satorusaka/Ongeki-Con/WAD assembly/STLs/WAD - Cover.3mf

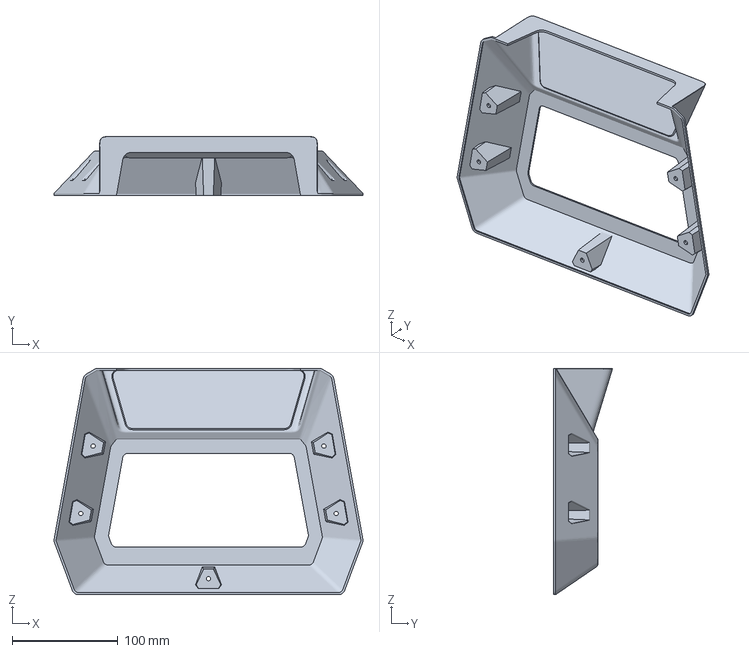
[picture p21: CAD file, 2023-08-07]
WAD assembly/STLs/WAD - Cover.3mf
292.7 x 55.8 x 214.4 mm
