satorusaka/Ongeki-Con/Swing assembly/STLs/Knob_L.3mf

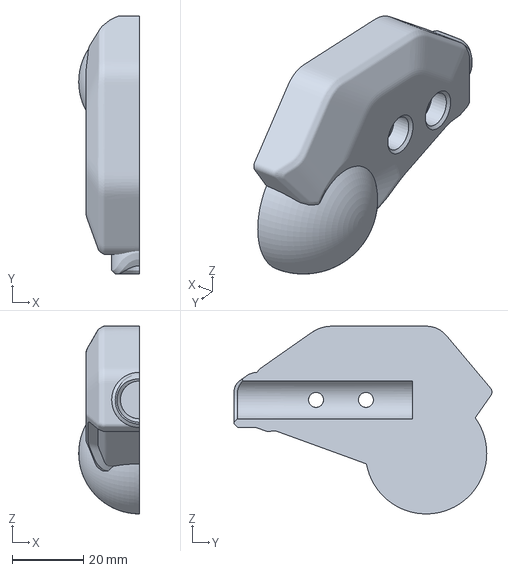
[picture p22: CAD file, 2023-09-01]
Swing assembly/STLs/Knob_L.3mf
17.0 x 72.3 x 52.7 mm
