satorusaka/Ongeki-Con/Swing assembly/STLs/T-Coupler.3mf

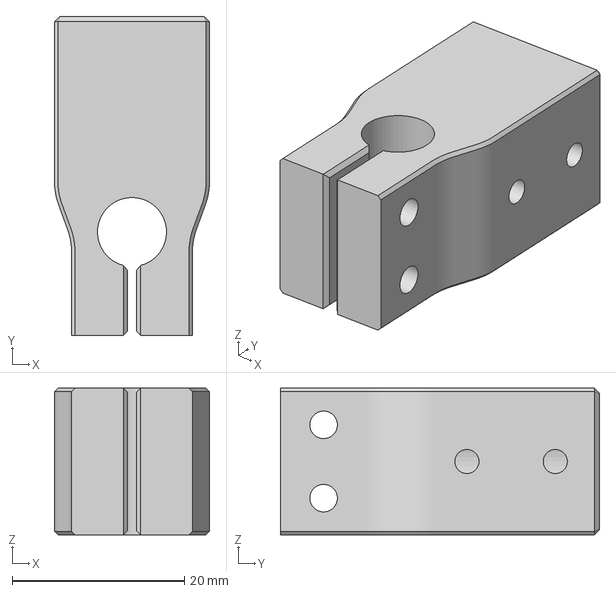
[picture p23: CAD file, 2023-09-01]
Swing assembly/STLs/T-Coupler.3mf
18.0 x 37.0 x 17.0 mm
